eigenco/LPT2MIDI/softmpu/PIC.C

/*
 *  Copyright (C) 2002-2012  The DOSBox Team
 *  Copyright (C) 2013-2014  bjt
 *
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
 *  You should have received a copy of the GNU General Public License
 *  along with this program; if not, write to the Free Software
 *  Foundation, Inc., 59 Temple Place - Suite 330, Boston, MA 02111-1307, USA.
 */

/*
 * ------------------------------------------
 * SoftMPU by bjt - Software MPU-401 Emulator
 * ------------------------------------------
 *
 * Based on original pic.c from DOSBox
 *
 */

/* SOFTMPU: Moved exported functions & types to header */
#include "export.h"

void MPU401_Event(void);
void MPU401_ResetDone(void);
void MPU401_EOIHandler(void);

/* SOFTMPU: Event countdown timers */
static Bitu event_countdown[NUM_EVENTS];
extern Bitu MIDI_sysex_delay; /* SOFTMPU: Initialised in midi.c */

/* SOFTMPU: Interrupt management functions */
void PIC_ActivateIRQ(Bitu sbport)
{
        /* Simulate MPU interrupts using a Sound Blaster (or compatible) */
        _asm
        {
                        mov     dx,sbport
                        add     dx,0Ch                  ; Select DSP command port
                        mov     al,0F2h                 ; DSP cmd 0xF2 = Force 8-bit IRQ
                        out     dx,al                   ; Raise IRQ
        }
}

void PIC_DeActivateIRQ(Bitu sbport)
{
        /* Acknowledge (lower) the SB interrupt by reading the status port */
        _asm
        {
                        mov     dx,sbport
                        add     dx,0Eh                  ; Select DSP read port
                        in      al,dx                   ; Acknowledge IRQ
        }
}

void PIC_SetIRQMask(Bitu irq, bool masked)
{
        const Bit8u t=irq>7?(irq-8):irq;
        const Bit8u mask=~(1<<t);
        const Bitu statusport=irq>7?0xA1:0x21;

        _asm
        {
                        pushf
                        cli                             ; No interrupts while progamming PIC
                        mov     dx,statusport
                        mov     bl,mask
                        in      al,dx
                        and     al,bl                   ; Clear bit
                        cmp     masked,0
                        je      SetMask
                        xor     bl,0FFh                 ; Invert mask
                        or      al,bl
        SetMask:        jmp     SHORT $+2               ; Enforce short pause between read & write
                        out     dx,al                   ; Set new mask
                        popf                            ; Enable interrupts
        }
}

void PIC_AddEvent(EventID event, Bitu delay)
{
        /* Dispatch event immediately on zero delay */
        /* Watch out for blocking loops here... */
        if (delay==0)
        {
                switch (event)
                {
                case MPU_EVENT:
                        /* Don't dispatch immediately as we'll enter an
                        infinite loop if tempo is high enough */
                        delay=1; /* Enforce minimum delay */
                        break;
                case RESET_DONE:
                        MPU401_ResetDone();
                        break;
                case EOI_HANDLER:
                        MPU401_EOIHandler();
                        break;
                default:
                        break;
                }
        }

        /* SOFTMPU: Set the countdown timer */
        event_countdown[event]=delay;
}

void PIC_RemoveEvents(EventID event)
{
        /* SOFTMPU: Zero the countdown timer (disable event) */
        event_countdown[event]=0;
}

void PIC_Init(void)
{
        Bitu i;

        /* SOFTMPU: Zero countdown timers */
        for (i=0;i<NUM_EVENTS;i++)
        {
                PIC_RemoveEvents(i);
        }
}

void PIC_Update(bool blocking)
{
        Bitu i;
        unsigned short xx, yy, zz;

        if (blocking)
        {
                /* SOFTMPU: Manually time an RTC tick */
                _asm
                {
                                ; Bit 4 of port 061h toggles every 15.085us
                                mov     cx,17                   ; Assume 4kHz RTC
                                in      al,061h
                                and     al,010h                 ; Get initial value
                                mov     bl,al
                TestPort:       in      al,061h
                                and     al,010h
                                cmp     al,bl
                                je      TestPort                ; Loop until toggled
                                xor     bl,010h                 ; Invert
                                loop    TestPort
                }
        }

        /* SOFTMPU: Decrement sysex delay used in midi.c */
        if (MIDI_sysex_delay > 0)
        {
                MIDI_sysex_delay--;
                //for(xx=0; xx<65535; xx++);
        }

        /* SOFTMPU: Decrement countdown timers and dispatch as needed */
        for (i=0;i<NUM_EVENTS;i++)
        {
                if (event_countdown[i] > 0)
                {
                        event_countdown[i]--;

                        if (event_countdown[i]==0)
                        {
                                /* Dispatch */
                                switch (i)
                                {
                                        case MPU_EVENT:
                                                MPU401_Event();
                                                break;
                                        case RESET_DONE:
                                                MPU401_ResetDone();
                                                break;
                                        case EOI_HANDLER:
                                                MPU401_EOIHandler();
                                                break;
                                        default:
                                                break;
                                }
                        }
                }
        }
}
